Unriell/ZUMJunior/images/examples/Multi.PNG

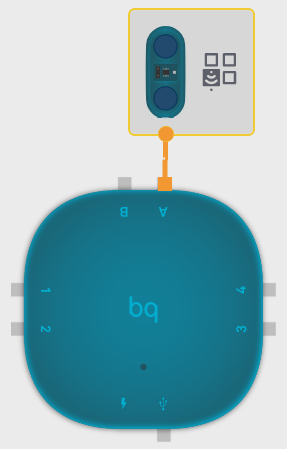
images/examples/Multi.PNG
