Unriell/ZUMJunior/images/examples/Multi_USB.PNG

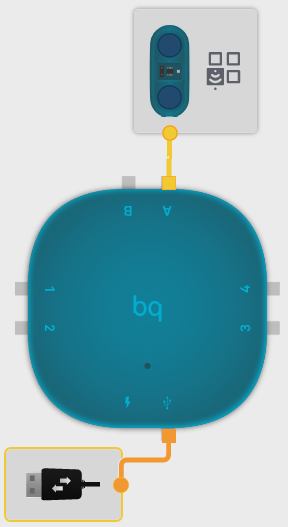
images/examples/Multi_USB.PNG
